wyolum/MC60/data/Screenshot from 2018-04-23 21-39-15.png

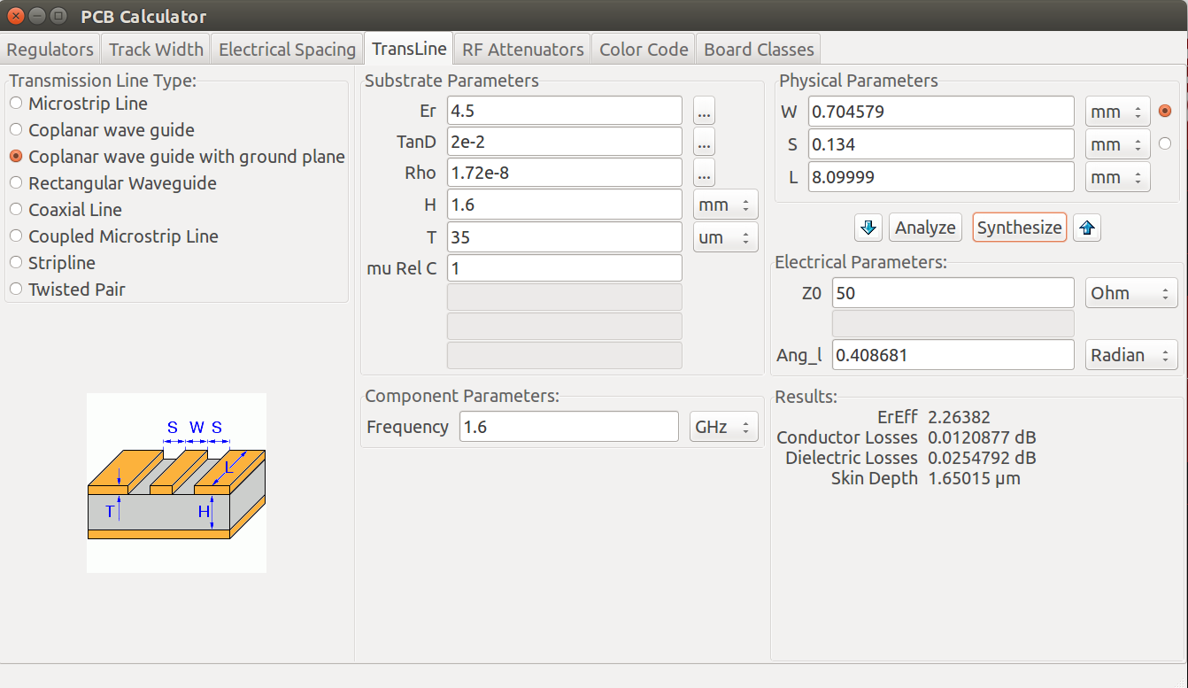
data/Screenshot from 2018-04-23 21-39-15.png
