wyolum/MC60/data/trrs-diagram3.jpg

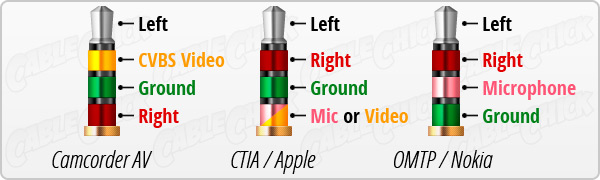
data/trrs-diagram3.jpg
