wyolum/MC60/data/trrs-diagram4.jpg

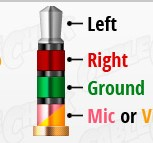
data/trrs-diagram4.jpg
