wyolum/MC60/kicad/mc60_images/mc60-06.png

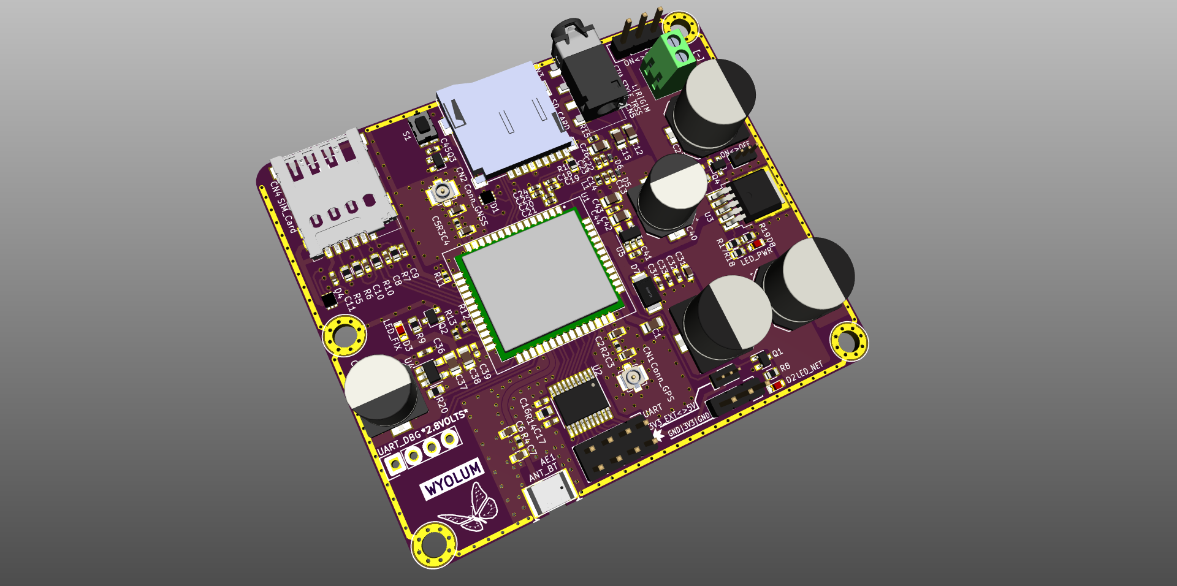
kicad/mc60_images/mc60-06.png
