wyolum/MC60/kicad/3d_modules/R_0603.step

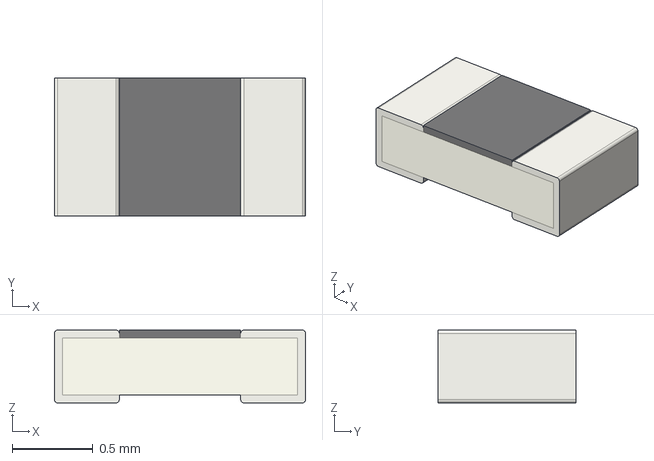
[picture p25: CAD file, 2018-05-02]
kicad/3d_modules/R_0603.step
1.55 x 0.85 x 0.45 mm
