wyolum/MC60/kicad/3d_modules/conn_rf_uFL_3450020P1.step

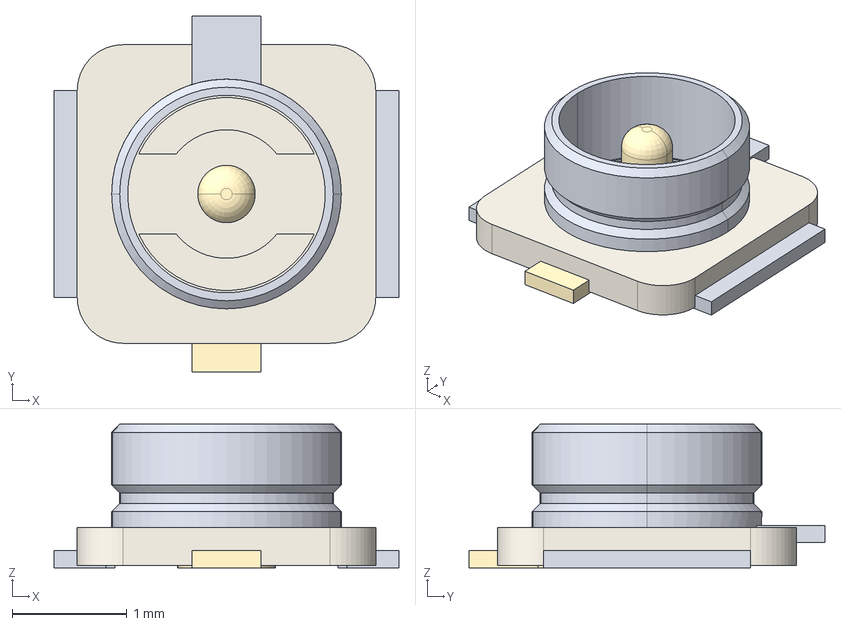
[picture p26: CAD file, 2018-05-02]
kicad/3d_modules/conn_rf_uFL_3450020P1.step
3.00 x 3.10 x 1.25 mm
