wyolum/MC60/kicad/3d_modules/Pin_Header_Straight_2x04_Pitch254mm.step

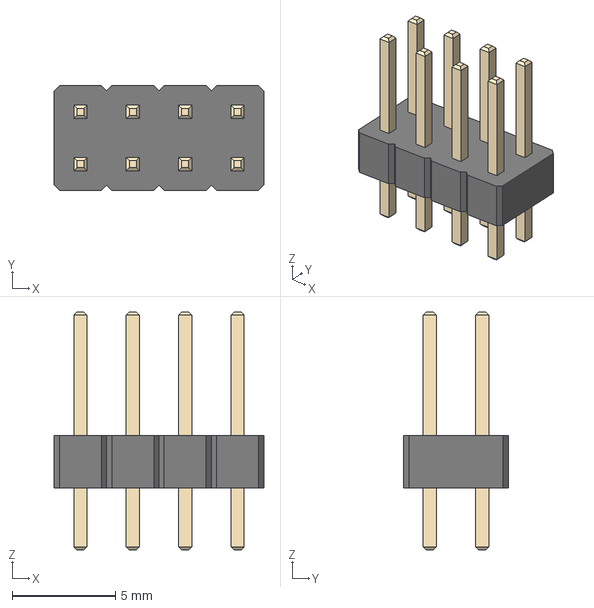
[picture p27: CAD file, 2018-05-02]
kicad/3d_modules/Pin_Header_Straight_2x04_Pitch254mm.step
10.2 x 5.08 x 11.5 mm
