wyolum/MC60/kicad/3d_modules/diode_SOD923.step

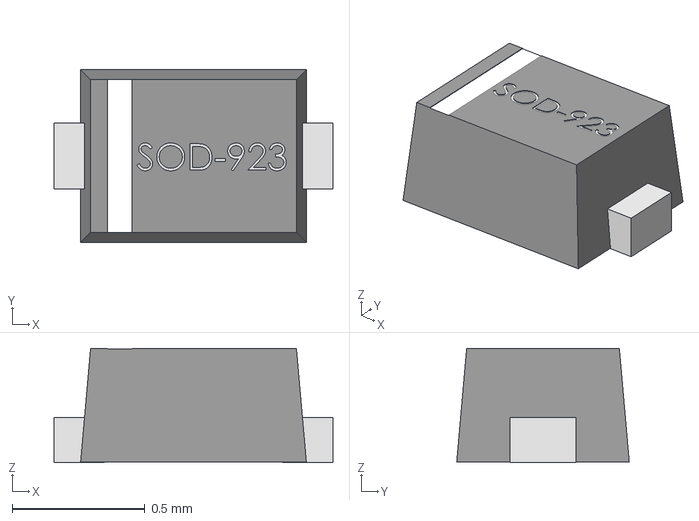
[picture p28: CAD file, 2018-05-02]
kicad/3d_modules/diode_SOD923.step
1.05 x 0.65 x 0.43 mm
