wyolum/MC60/kicad/3d_modules/sw_pb_smd.step

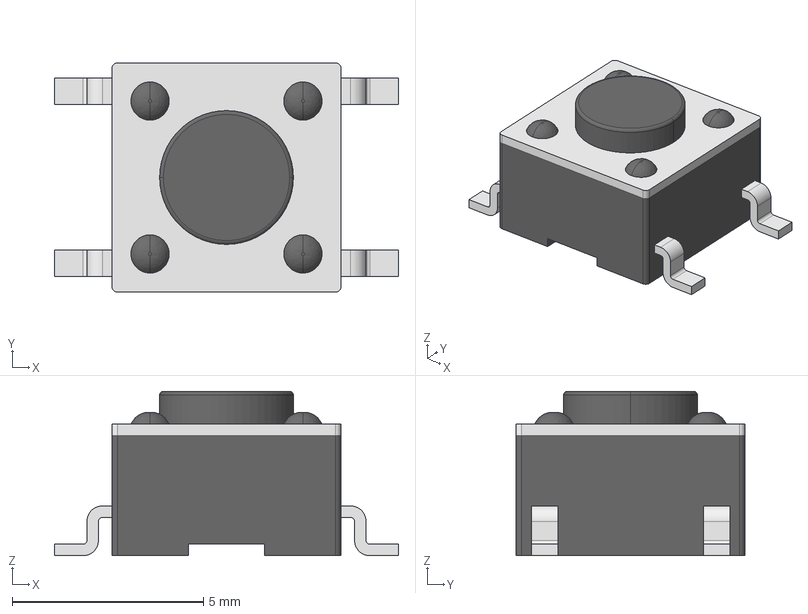
[picture p29: CAD file, 2018-05-02]
kicad/3d_modules/sw_pb_smd.step
9.00 x 6.00 x 4.30 mm
