wyolum/MC60/kicad/3d_modules/SLP1616P6_3D.step

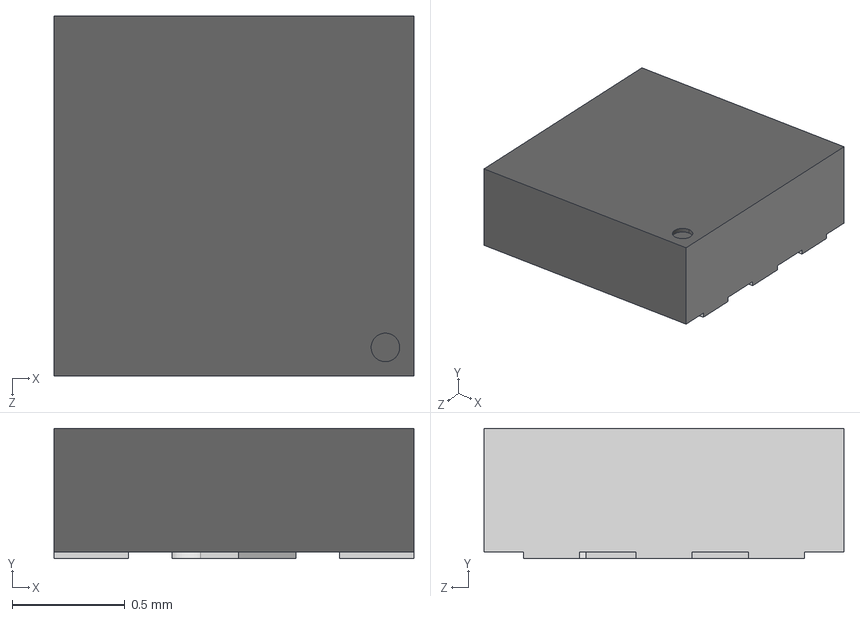
[picture p30: CAD file, 2018-05-02]
kicad/3d_modules/SLP1616P6_3D.step
1.60 x 0.58 x 1.60 mm
