wyolum/MC60/kicad/3d_modules/SOT_23_5.step

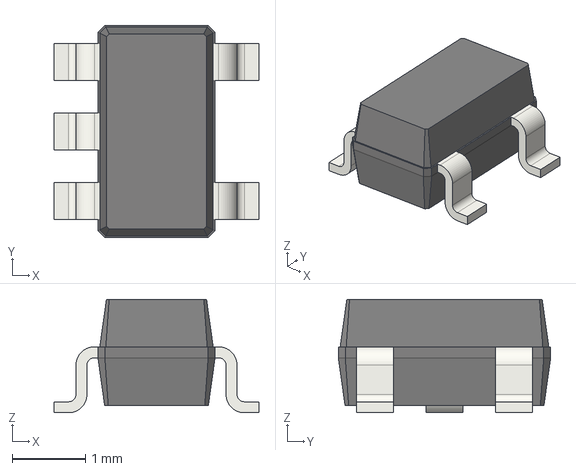
[picture p31: CAD file, 2018-05-02]
kicad/3d_modules/SOT_23_5.step
2.80 x 2.90 x 1.55 mm
