wyolum/MC60/kicad/3d_modules/C_0402.step

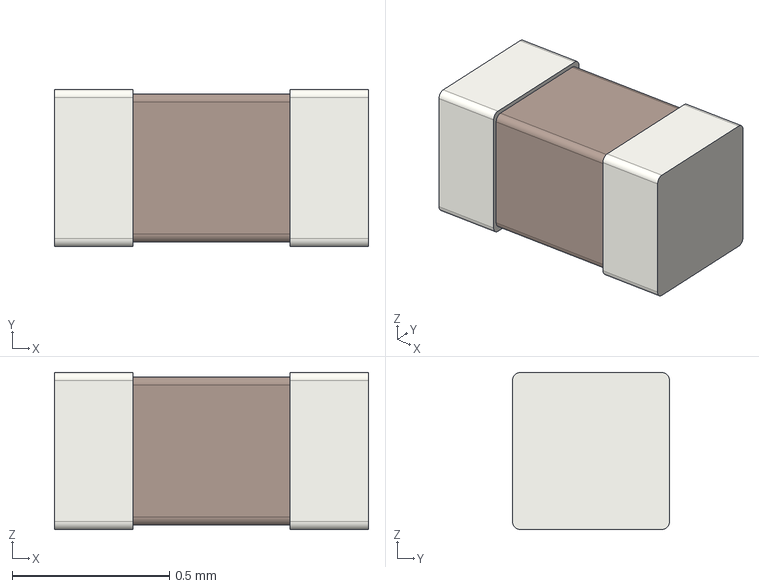
[picture p32: CAD file, 2018-05-02]
kicad/3d_modules/C_0402.step
1.00 x 0.5 x 0.5 mm
