wyolum/MC60/kicad/3d_modules/ant_bt_inpaq_5036.step

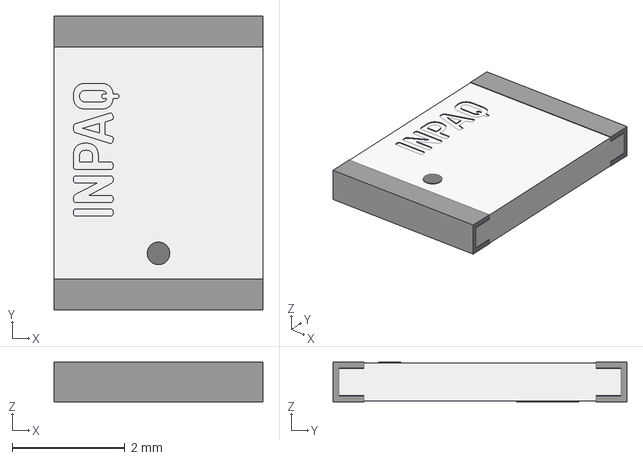
[picture p33: CAD file, 2018-05-02]
kicad/3d_modules/ant_bt_inpaq_5036.step
3.70 x 5.20 x 0.7 mm
