wyolum/MC60/kicad/3d_modules/conn_phoenix_MPT.step

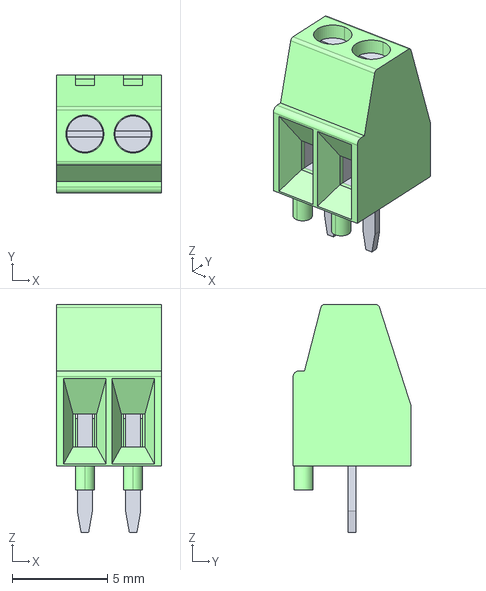
[picture p34: CAD file, 2018-05-02]
kicad/3d_modules/conn_phoenix_MPT.step
5.54 x 6.20 x 12.0 mm
