wyolum/MC60/kicad/3d_modules/Pin_Header_Straight_1x03_Pitch254mm.step

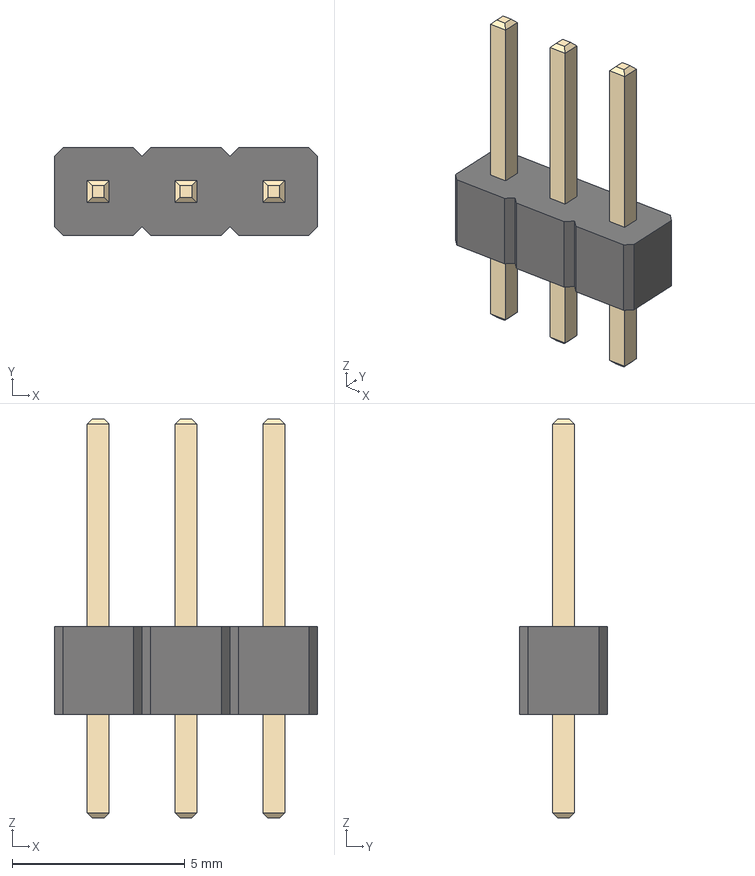
[picture p35: CAD file, 2018-05-02]
kicad/3d_modules/Pin_Header_Straight_1x03_Pitch254mm.step
7.62 x 2.54 x 11.5 mm
