wyolum/MC60/kicad/3d_modules/TSSOP_20_44x65mm_Pitch065mm.step

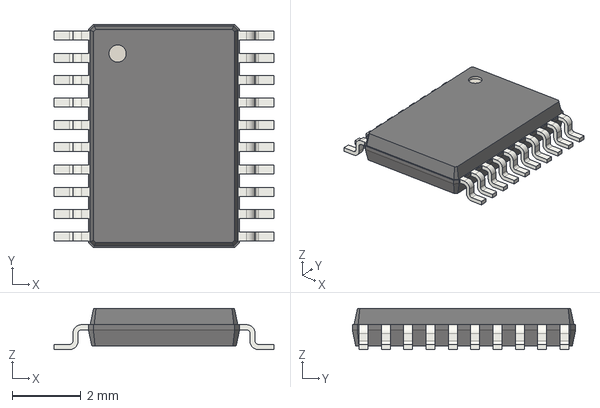
[picture p36: CAD file, 2018-05-02]
kicad/3d_modules/TSSOP_20_44x65mm_Pitch065mm.step
6.40 x 6.50 x 1.20 mm
