wyolum/MC60/kicad/3d_modules/conn_micro_SD_01.step

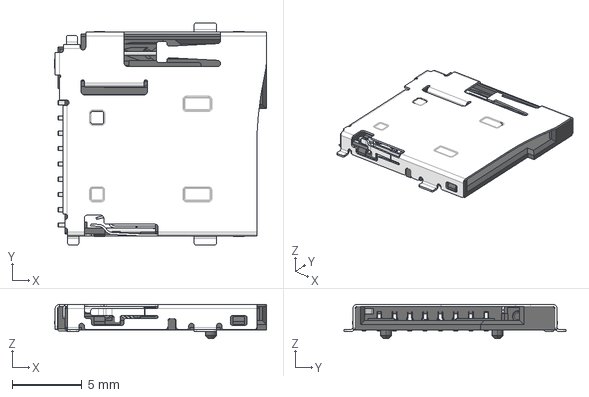
[picture p37: CAD file, 2018-05-02]
kicad/3d_modules/conn_micro_SD_01.step
15.2 x 16.0 x 2.45 mm
