wyolum/MC60/kicad/3d_modules/TO_252_5_TabPin3.step

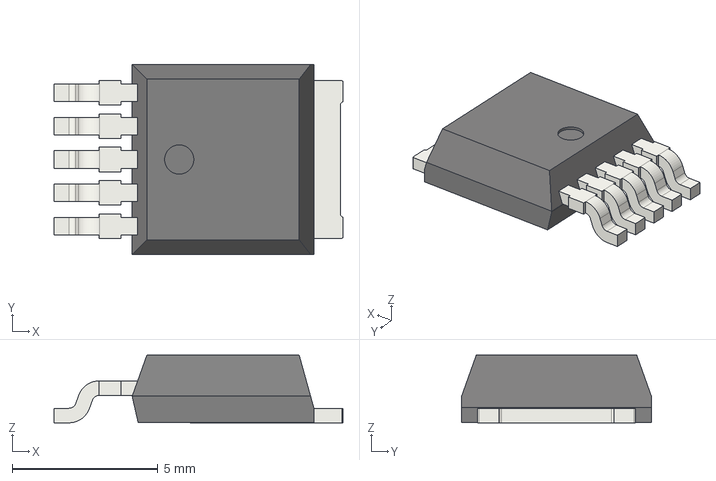
[picture p38: CAD file, 2018-05-02]
kicad/3d_modules/TO_252_5_TabPin3.step
9.90 x 6.50 x 2.32 mm
