wyolum/MC60/kicad/3d_modules/C_0603.step

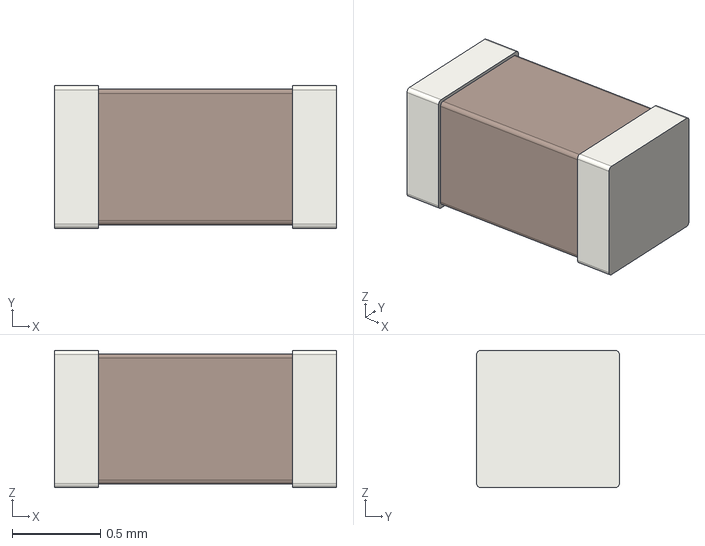
[picture p39: CAD file, 2018-05-02]
kicad/3d_modules/C_0603.step
1.60 x 0.81 x 0.78 mm
