wyolum/MC60/kicad/3d_modules/conn_trrs_320040003.step

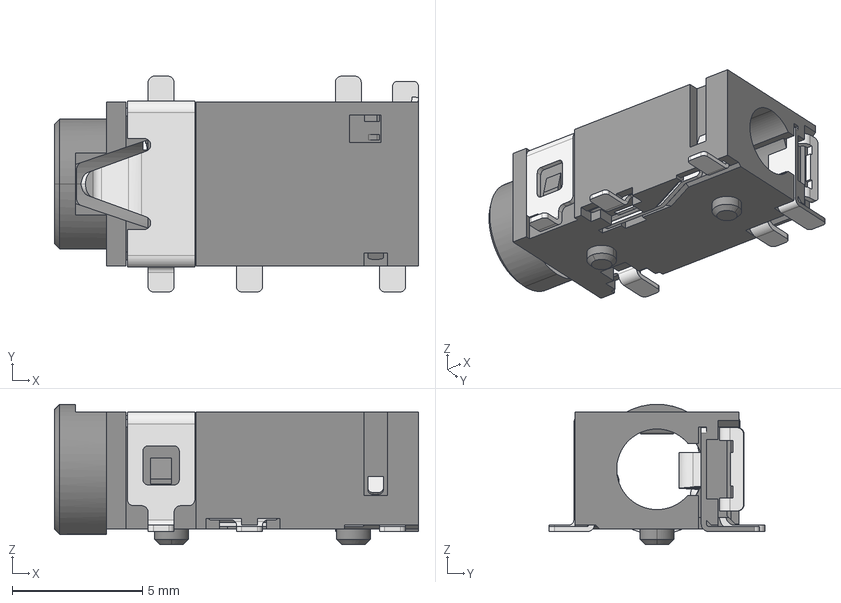
[picture p40: CAD file, 2018-05-02]
kicad/3d_modules/conn_trrs_320040003.step
14.0 x 8.30 x 5.40 mm
