wyolum/MC60/kicad/3d_modules/CUI_SJ-43514-SMT-TR.step

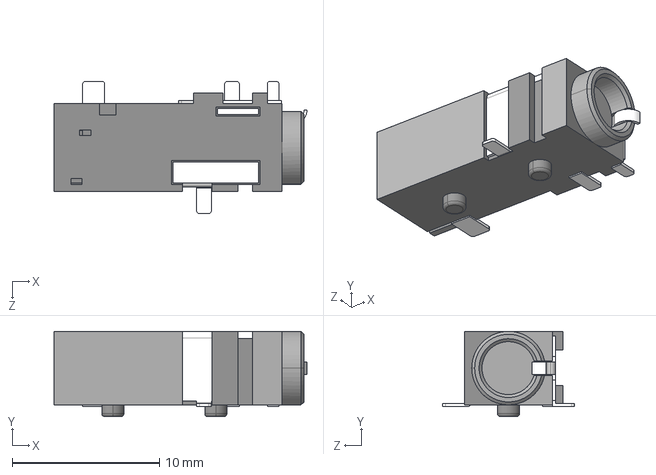
[picture p41: CAD file, 2018-04-20]
kicad/3d_modules/CUI_SJ-43514-SMT-TR.step
17.2 x 5.80 x 9.00 mm
