wyolum/MC60/kicad/mc60_pdf/mc60.pdf

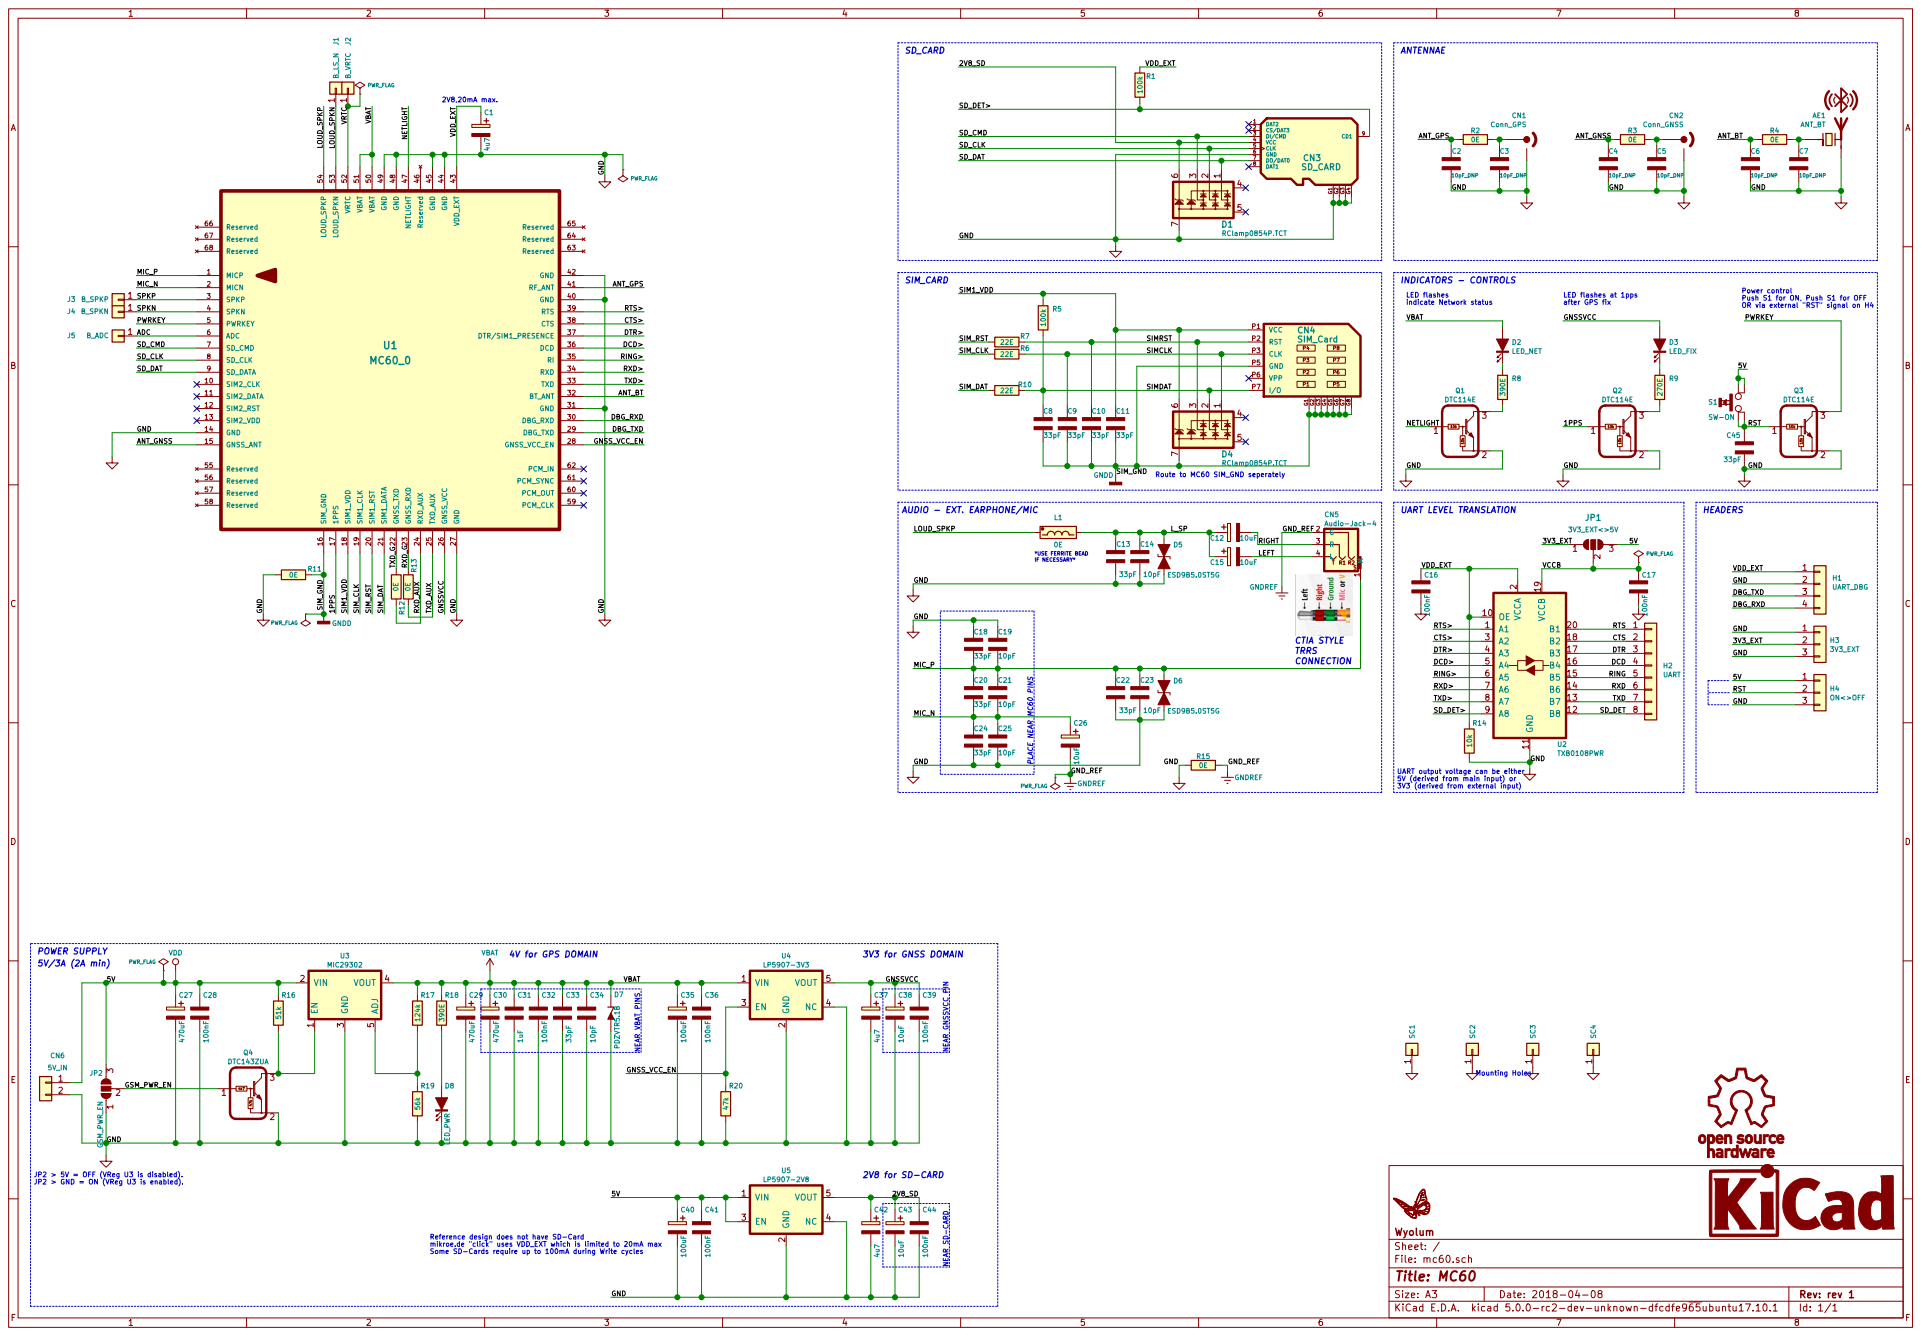
[picture p43: page 1]

Power control Push S1 for ON, Push S1 for OFF OR via external "RST" signal on H4

LED flashes at 1pps after GPS fix LED flashes

UART output voltage can be either 5V (derived from main input) or 3V3 (derived from external input)

JP2 > 5V = OFF (VReg U3 is disabled). JP2 > GND = ON (VReg U3 is enabled).

File: mc60.sch Sheet: / Wyolum

Reference design does not have SD-Card mikroe.de "click" uses VDD_EXT which is limited to 20mA max Some SD-Cards require up to 100mA during Write cycles
