wyolum/MC60/data/conn_trrs_320040003.pdf

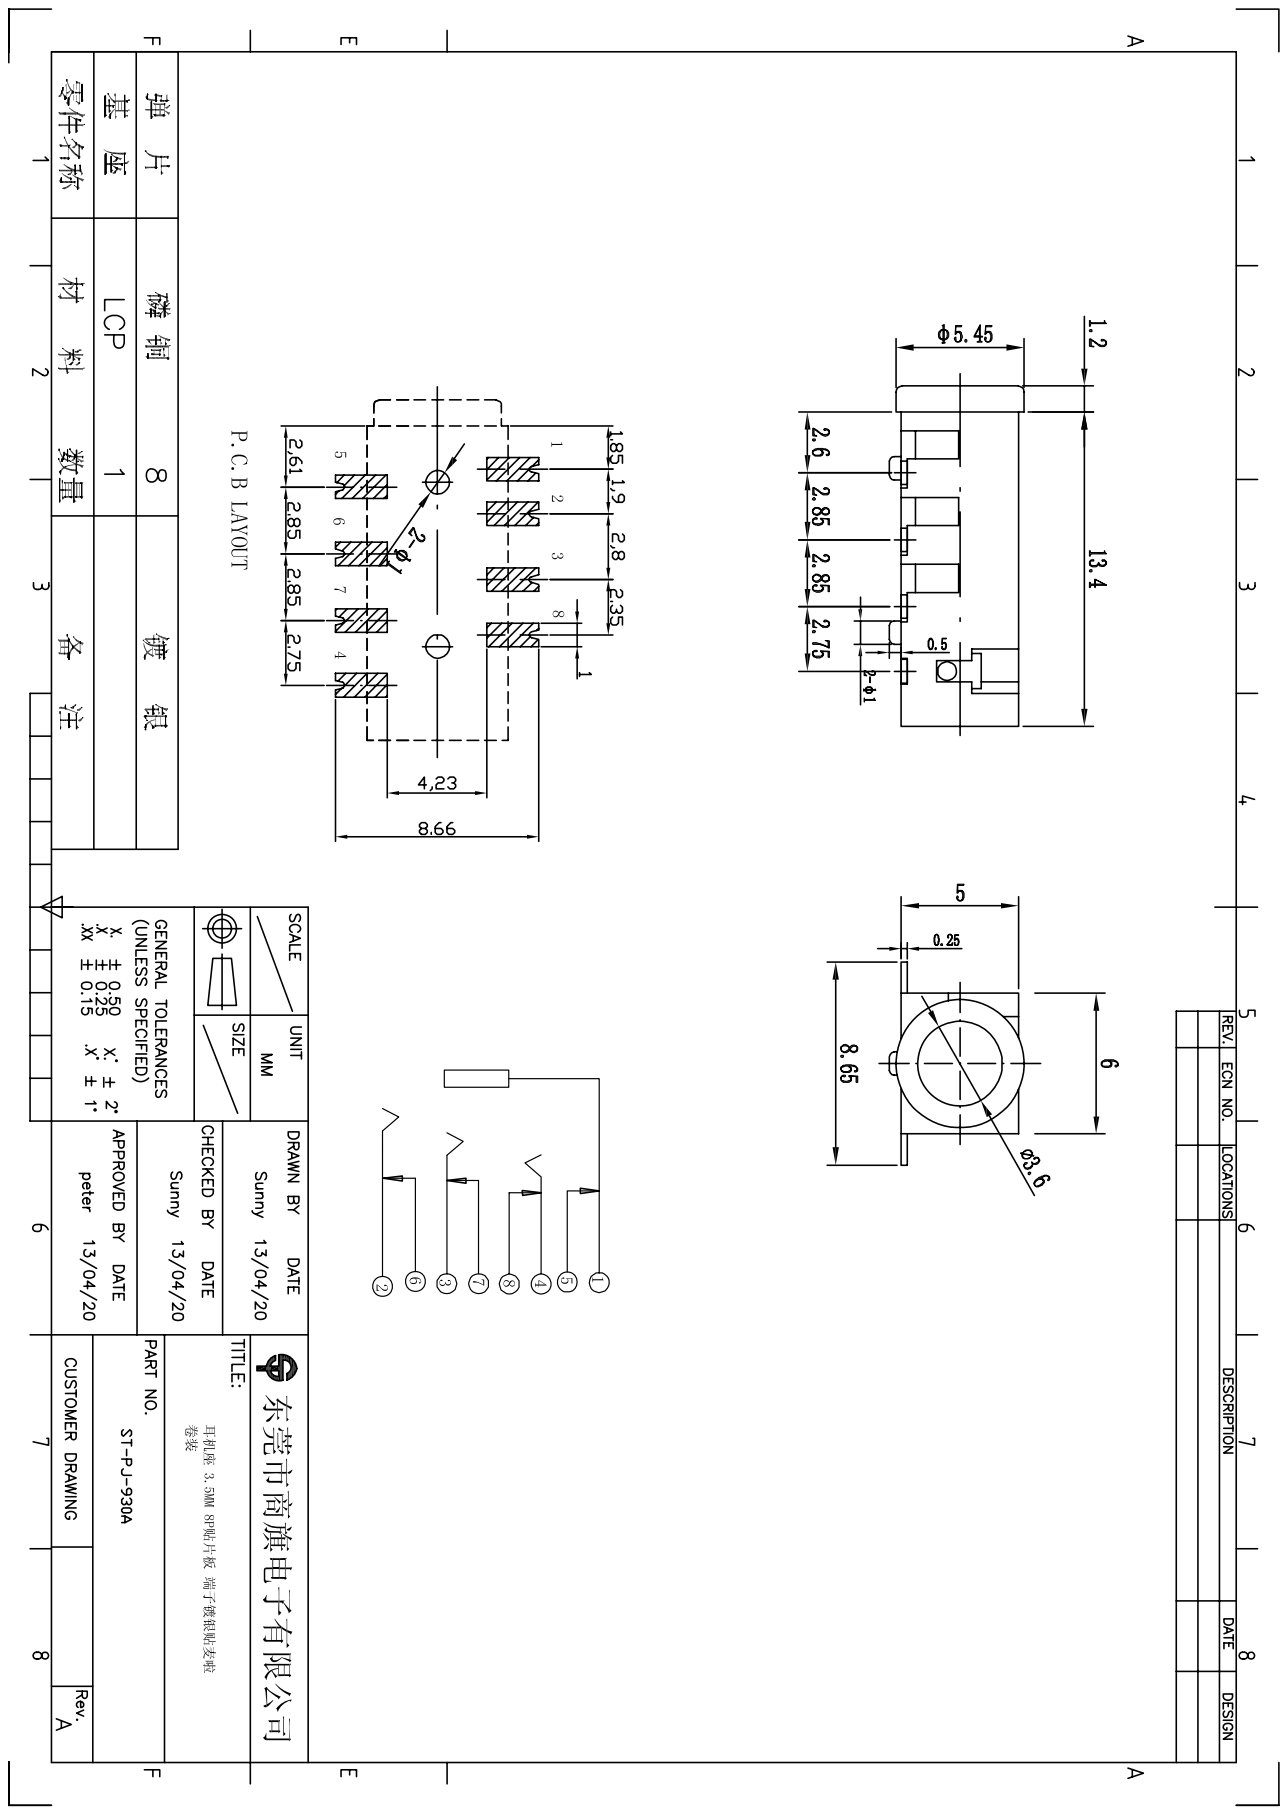
[picture p44: page 1]
