wyolum/MC60/kicad/mc60_pdf/mc60-B.Cu.pdf

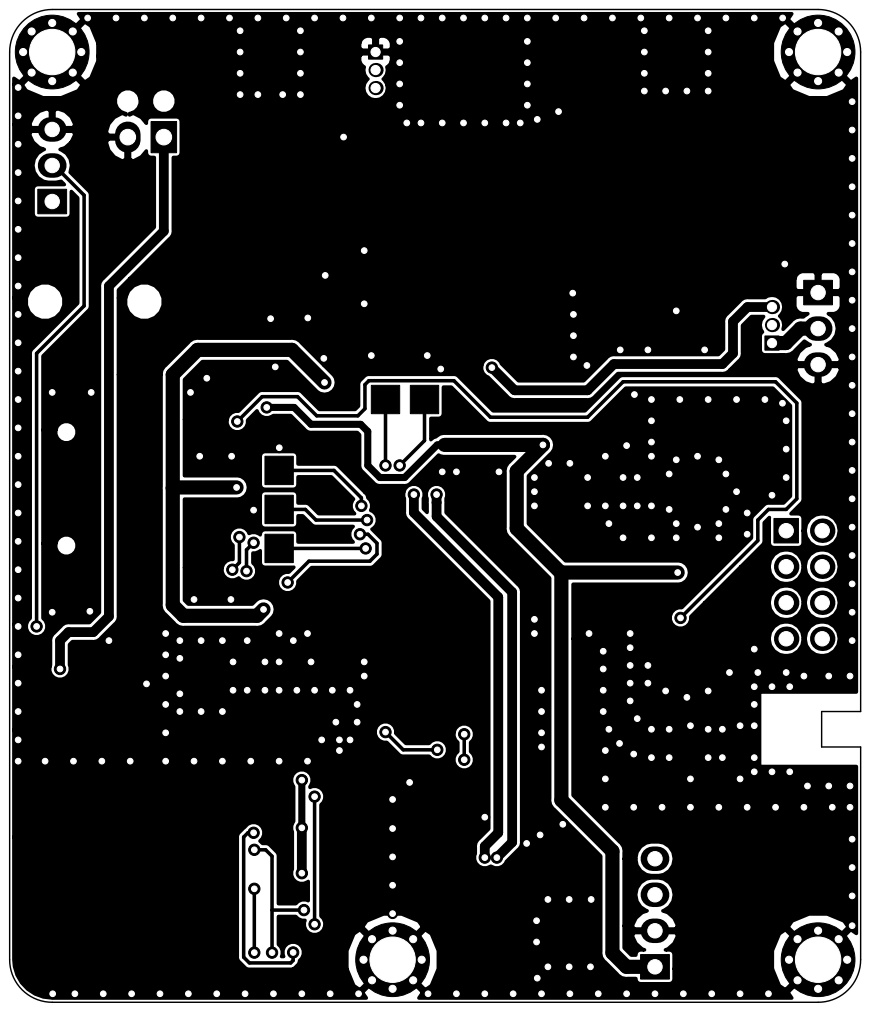
[picture p45: page 1]
