wyolum/MC60/kicad/mc60_pdf/mc60-B.SilkS.pdf

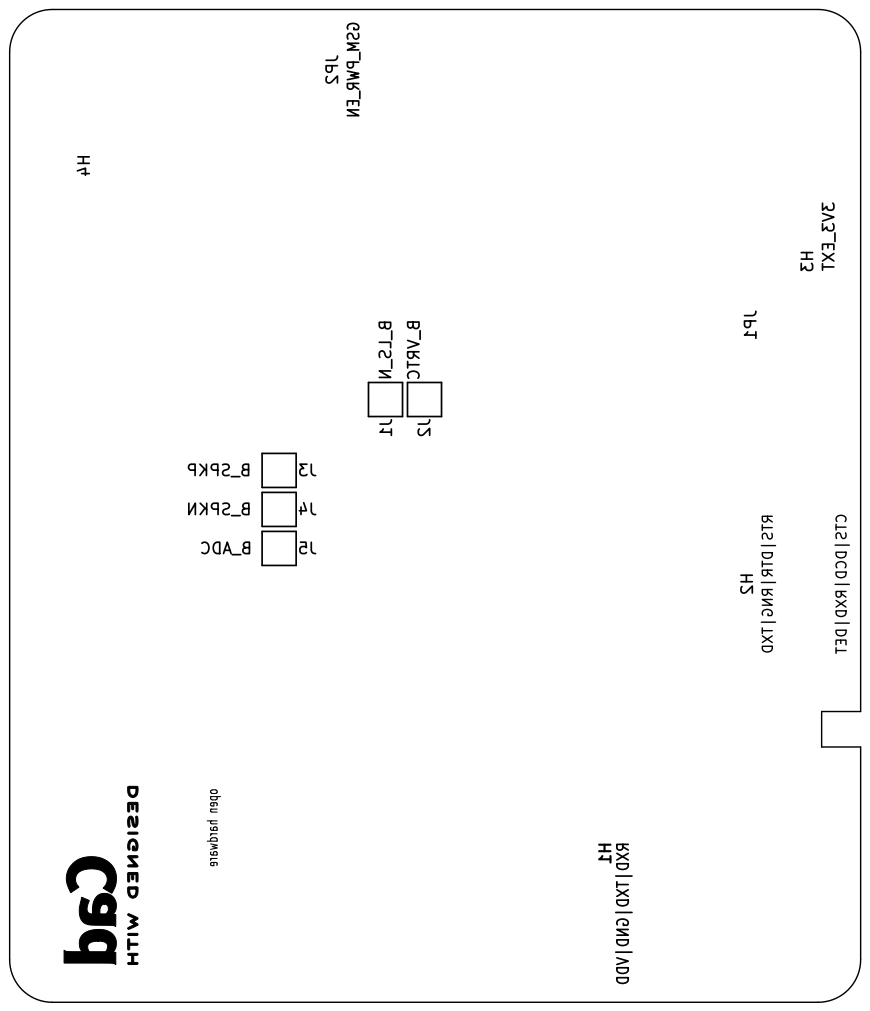
[picture p46: page 1]
