wyolum/MC60/kicad/mc60_pdf/mc60-Dwgs.User.pdf

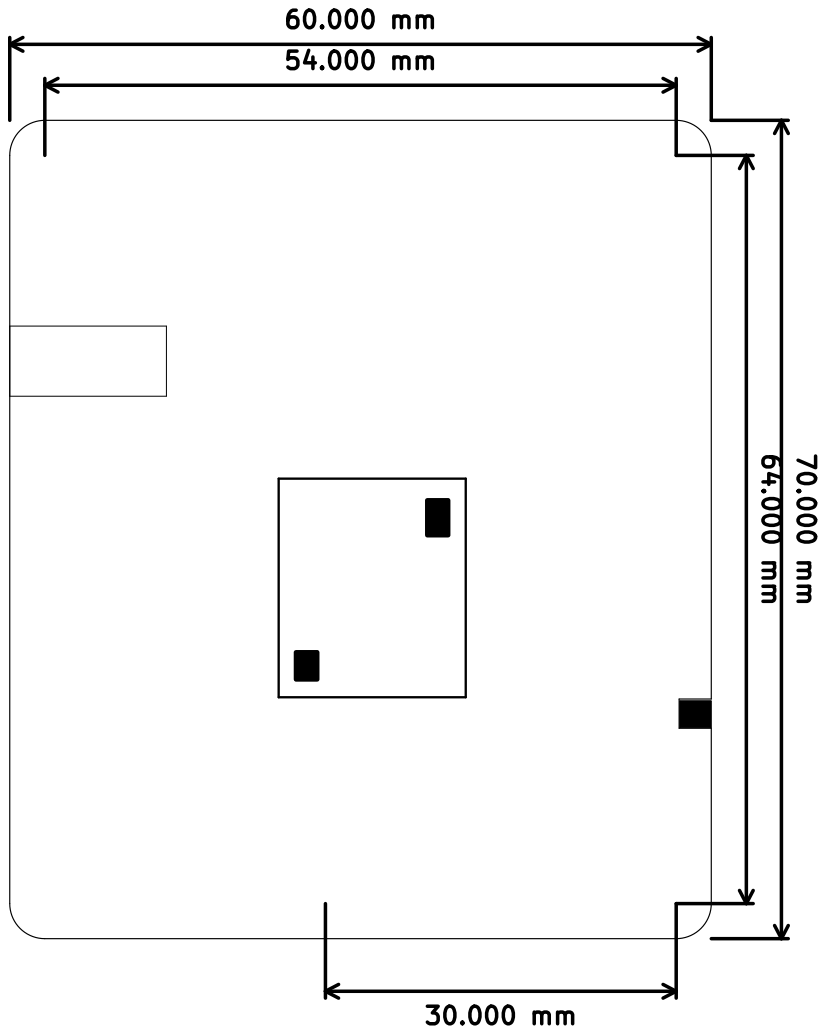
[picture p47: page 1]
