wyolum/MC60/kicad/mc60_pdf/mc60-F.Cu.pdf

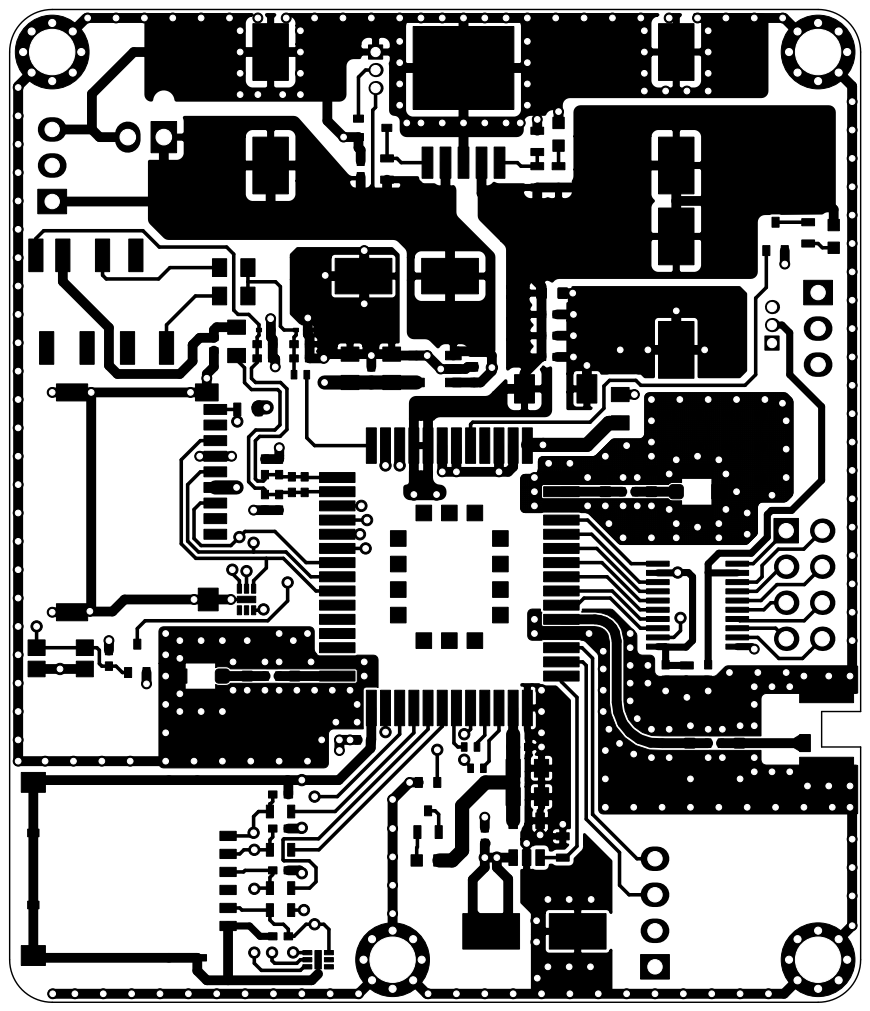
[picture p48: page 1]
