wyolum/MC60/kicad/mc60_pdf/mc60-F.Fab.pdf

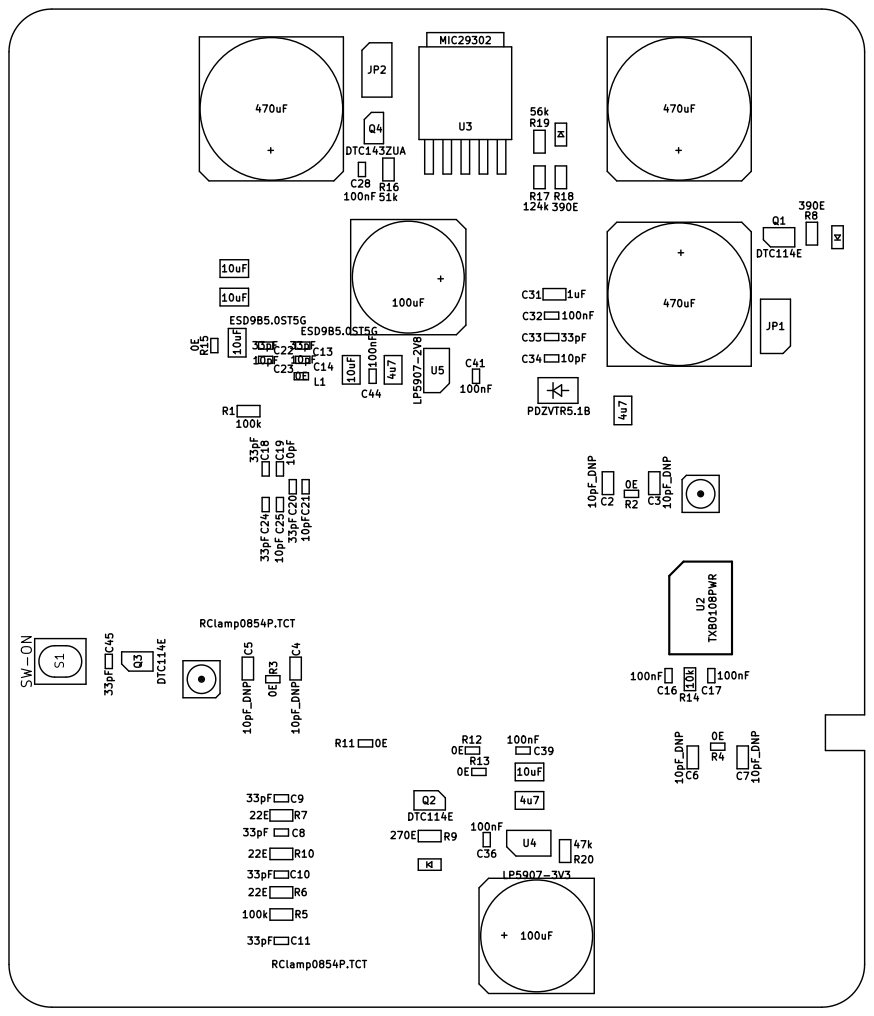
[picture p49: page 1]
