wyolum/MC60/kicad/mc60_pdf/mc60-F.SilkS.pdf

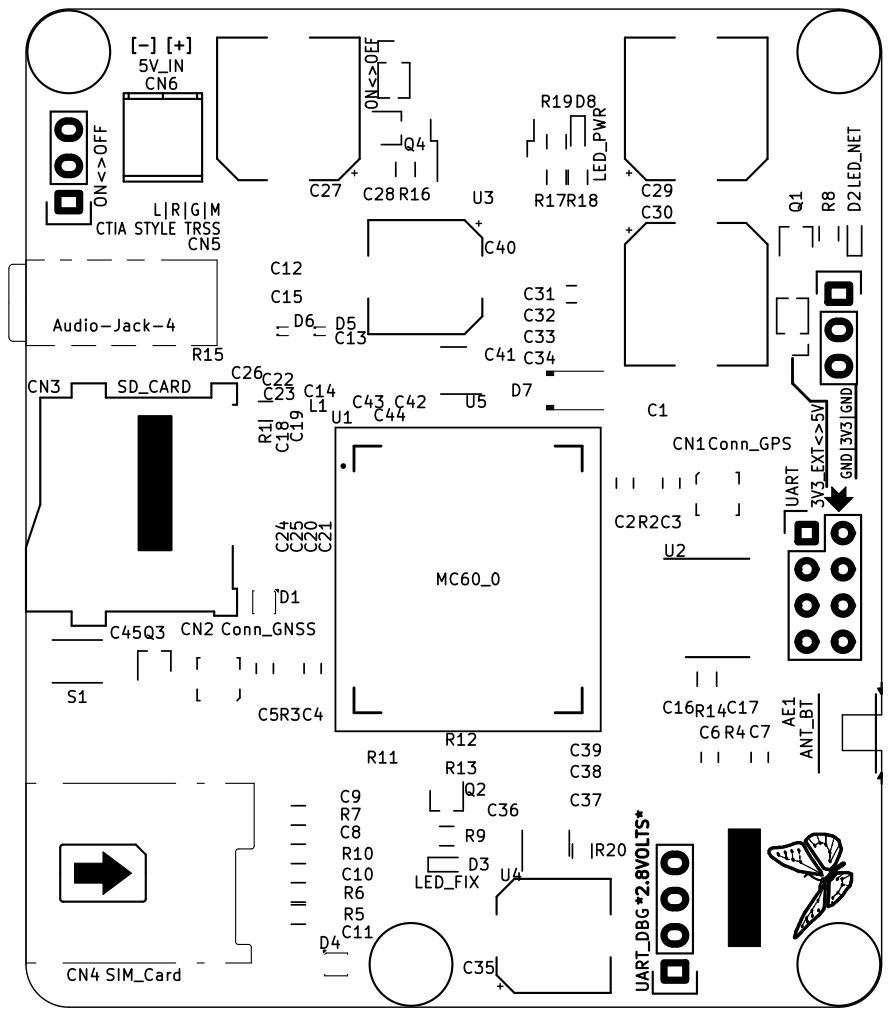
[picture p50: page 1]
